JJassonn69/PLFM_RADAR/9_Firmware/9_2_FPGA/tb/tb_uart_txrx.v

`timescale 1ns / 1ps
// ============================================================================
// AERIS-10 UART TX + RX Loopback Testbench
// ============================================================================
//
// Tests:
//   1. TX sends a byte, loopback wire feeds it to RX, verify RX output
//   2. Multiple bytes in sequence (0x00, 0x55, 0xAA, 0xFF, 0x42)
//   3. TX busy/done signals behave correctly
//   4. RX frame error detection (inject bad stop bit)
//   5. Back-to-back transmission without gaps
//
// Uses fast baud rate for simulation: CLK_FREQ=50MHz, BAUD_RATE=1_000_000
// (BAUD_DIV=50, one bit = 50 clock cycles, one byte ~= 500 cycles)
// ============================================================================

module tb_uart_txrx;

    // Use fast baud for simulation speed
    parameter CLK_FREQ  = 50_000_000;
    parameter BAUD_RATE = 1_000_000;
    parameter BAUD_DIV  = CLK_FREQ / BAUD_RATE;  // 50

    reg        clk;
    reg        reset_n;

    // TX signals
    reg  [7:0] tx_data;
    reg        tx_start;
    wire       txd;
    wire       tx_busy;
    wire       tx_done;

    // RX signals
    wire [7:0] rx_data;
    wire       rx_data_valid;
    wire       rx_frame_error;

    // Loopback wire (TX output -> RX input), with override for error injection
    reg        force_rxd;
    reg        use_force_rxd;
    wire       rxd_wire;
    assign rxd_wire = use_force_rxd ? force_rxd : txd;

    // Instantiate TX
    uart_tx #(
        .CLK_FREQ(CLK_FREQ),
        .BAUD_RATE(BAUD_RATE)
    ) u_tx (
        .clk(clk),
        .reset_n(reset_n),
        .tx_data(tx_data),
        .tx_start(tx_start),
        .txd(txd),
        .tx_busy(tx_busy),
        .tx_done(tx_done)
    );

    // Instantiate RX
    uart_rx #(
        .CLK_FREQ(CLK_FREQ),
        .BAUD_RATE(BAUD_RATE)
    ) u_rx (
        .clk(clk),
        .reset_n(reset_n),
        .rxd(rxd_wire),
        .rx_data(rx_data),
        .rx_data_valid(rx_data_valid),
        .rx_frame_error(rx_frame_error)
    );

    // Clock: 50 MHz -> 20 ns period
    initial clk = 0;
    always #10 clk = ~clk;

    // Test counters
    integer pass_count;
    integer fail_count;

    // Task: send one byte and wait for TX to finish
    task send_byte;
        input [7:0] data;
        begin
            @(posedge clk);
            tx_data  <= data;
            tx_start <= 1'b1;
            @(posedge clk);
            tx_start <= 1'b0;
            // Wait for tx_done
            @(posedge tx_done);
            @(posedge clk);
        end
    endtask

    // Task: wait for RX valid pulse with timeout
    // First waits until rx_data_valid is LOW (in case previous pulse still active),
    // then waits for the next rising edge of rx_data_valid.
    task wait_rx_valid;
        output       got_valid;
        output [7:0] got_data;
        output       got_error;
        integer timeout;
        begin
            got_valid = 0;
            got_data  = 8'd0;
            got_error = 0;
            timeout   = 0;
            // Wait for any existing valid pulse to clear
            while ((rx_data_valid || rx_frame_error) && timeout < (BAUD_DIV * 2)) begin
                @(posedge clk);
                timeout = timeout + 1;
            end
            // Now wait for the next valid pulse
            timeout = 0;
            while (!rx_data_valid && !rx_frame_error && timeout < (BAUD_DIV * 15)) begin
                @(posedge clk);
                timeout = timeout + 1;
            end
            if (rx_data_valid) begin
                got_valid = 1;
                got_data  = rx_data;
            end
            if (rx_frame_error) begin
                got_error = 1;
            end
        end
    endtask

    // Main test sequence
    reg        got_v;
    reg [7:0]  got_d;
    reg        got_e;

    initial begin
        $dumpfile("tb_uart_txrx.vcd");
        $dumpvars(0, tb_uart_txrx);

        pass_count    = 0;
        fail_count    = 0;
        reset_n       = 0;
        tx_data       = 8'd0;
        tx_start      = 0;
        use_force_rxd = 0;
        force_rxd     = 1;

        // Reset
        repeat (10) @(posedge clk);
        reset_n = 1;
        repeat (5) @(posedge clk);

        // -------------------------------------------------------
        // TEST 1: TX idle state
        // -------------------------------------------------------
        if (txd == 1'b1 && tx_busy == 1'b0) begin
            $display("[PASS] TX idle: txd=1, busy=0");
            pass_count = pass_count + 1;
        end else begin
            $display("[FAIL] TX idle: txd=%b, busy=%b (expected 1, 0)", txd, tx_busy);
            fail_count = fail_count + 1;
        end

        // -------------------------------------------------------
        // TEST 2: Send 0x55 (alternating bits) — loopback verify
        // -------------------------------------------------------
        fork
            send_byte(8'h55);
            wait_rx_valid(got_v, got_d, got_e);
        join

        if (got_v && got_d == 8'h55 && !got_e) begin
            $display("[PASS] Loopback 0x55: received 0x%02h", got_d);
            pass_count = pass_count + 1;
        end else begin
            $display("[FAIL] Loopback 0x55: valid=%b data=0x%02h error=%b", got_v, got_d, got_e);
            fail_count = fail_count + 1;
        end

        // Wait for line to settle
        repeat (BAUD_DIV * 2) @(posedge clk);

        // -------------------------------------------------------
        // TEST 3: Send 0x00 (all zeros)
        // -------------------------------------------------------
        fork
            send_byte(8'h00);
            wait_rx_valid(got_v, got_d, got_e);
        join

        if (got_v && got_d == 8'h00 && !got_e) begin
            $display("[PASS] Loopback 0x00: received 0x%02h", got_d);
            pass_count = pass_count + 1;
        end else begin
            $display("[FAIL] Loopback 0x00: valid=%b data=0x%02h error=%b", got_v, got_d, got_e);
            fail_count = fail_count + 1;
        end

        repeat (BAUD_DIV * 2) @(posedge clk);

        // -------------------------------------------------------
        // TEST 4: Send 0xAA (alternate pattern)
        // -------------------------------------------------------
        fork
            send_byte(8'hAA);
            wait_rx_valid(got_v, got_d, got_e);
        join

        if (got_v && got_d == 8'hAA && !got_e) begin
            $display("[PASS] Loopback 0xAA: received 0x%02h", got_d);
            pass_count = pass_count + 1;
        end else begin
            $display("[FAIL] Loopback 0xAA: valid=%b data=0x%02h error=%b", got_v, got_d, got_e);
            fail_count = fail_count + 1;
        end

        repeat (BAUD_DIV * 2) @(posedge clk);

        // -------------------------------------------------------
        // TEST 5: Send 0xFF (all ones)
        // -------------------------------------------------------
        fork
            send_byte(8'hFF);
            wait_rx_valid(got_v, got_d, got_e);
        join

        if (got_v && got_d == 8'hFF && !got_e) begin
            $display("[PASS] Loopback 0xFF: received 0x%02h", got_d);
            pass_count = pass_count + 1;
        end else begin
            $display("[FAIL] Loopback 0xFF: valid=%b data=0x%02h error=%b", got_v, got_d, got_e);
            fail_count = fail_count + 1;
        end

        repeat (BAUD_DIV * 2) @(posedge clk);

        // -------------------------------------------------------
        // TEST 6: Send 0x42 ('B')
        // -------------------------------------------------------
        fork
            send_byte(8'h42);
            wait_rx_valid(got_v, got_d, got_e);
        join

        if (got_v && got_d == 8'h42 && !got_e) begin
            $display("[PASS] Loopback 0x42: received 0x%02h", got_d);
            pass_count = pass_count + 1;
        end else begin
            $display("[FAIL] Loopback 0x42: valid=%b data=0x%02h error=%b", got_v, got_d, got_e);
            fail_count = fail_count + 1;
        end

        repeat (BAUD_DIV * 2) @(posedge clk);

        // -------------------------------------------------------
        // TEST 7: TX busy flag asserts during transmission
        // -------------------------------------------------------
        @(posedge clk);
        tx_data  <= 8'hBE;
        tx_start <= 1'b1;
        @(posedge clk);
        tx_start <= 1'b0;

        // Check busy goes HIGH within a few cycles
        repeat (2) @(posedge clk);
        if (tx_busy == 1'b1) begin
            $display("[PASS] TX busy asserts during send");
            pass_count = pass_count + 1;
        end else begin
            $display("[FAIL] TX busy not asserted during send");
            fail_count = fail_count + 1;
        end

        // Wait for completion
        @(posedge tx_done);
        @(posedge clk);

        // Check busy clears
        @(posedge clk);
        if (tx_busy == 1'b0) begin
            $display("[PASS] TX busy clears after done");
            pass_count = pass_count + 1;
        end else begin
            $display("[FAIL] TX busy still asserted after done");
            fail_count = fail_count + 1;
        end

        // Wait for RX to finish receiving the 0xBE
        repeat (BAUD_DIV * 5) @(posedge clk);

        // -------------------------------------------------------
        // TEST 8: Frame error detection (inject bad stop bit)
        // -------------------------------------------------------
        // We'll manually drive the rxd line with a bad frame
        use_force_rxd = 1;
        force_rxd     = 1;  // Idle
        repeat (BAUD_DIV * 2) @(posedge clk);

        // Start bit
        force_rxd = 0;
        repeat (BAUD_DIV) @(posedge clk);

        // 8 data bits (send 0xAA = 10101010 LSB-first)
        force_rxd = 0; repeat (BAUD_DIV) @(posedge clk);  // bit 0 = 0
        force_rxd = 1; repeat (BAUD_DIV) @(posedge clk);  // bit 1 = 1
        force_rxd = 0; repeat (BAUD_DIV) @(posedge clk);  // bit 2 = 0
        force_rxd = 1; repeat (BAUD_DIV) @(posedge clk);  // bit 3 = 1
        force_rxd = 0; repeat (BAUD_DIV) @(posedge clk);  // bit 4 = 0
        force_rxd = 1; repeat (BAUD_DIV) @(posedge clk);  // bit 5 = 1
        force_rxd = 0; repeat (BAUD_DIV) @(posedge clk);  // bit 6 = 0
        force_rxd = 1; repeat (BAUD_DIV) @(posedge clk);  // bit 7 = 1

        // BAD stop bit (LOW instead of HIGH)
        force_rxd = 0;
        repeat (BAUD_DIV) @(posedge clk);

        // Return to idle
        force_rxd = 1;

        // Check for frame error
        repeat (BAUD_DIV * 2) @(posedge clk);
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
